cnobile2012/Li-IonBatteryProtection/LTSpice/Li-IonBatteryProtection.asc

C1: cap; 0.1µf
C2: cap; 0.22µf
C3: cap; 0.001µf
C4: cap; 47µf
D1: schottky; 1N5819
D2: schottky; 1N5819
D3: schottky; 1N5819
D4: schottky; 1N5819
Q1: npn2; 2N2222
Q2: npn2; 2N2222
Q3: npn2; 2N2222
Q4: npn2; 2N2222
Q5: npn2; 2N2222
Q6: IRF540; irf540n
R1: res; 10k
R2: res; 1k; tol=1 pwr=0.1
R3: res; 620k; tol=1 pwr=0.1
R4: res; 47k
R5: res; 100k; tol=1 pwr=0.1
R6: res; 100
R7: res; 120
R8: res; 10k
R9: res; 620k
R10: res; 1k
R11: res; 47k
R12: res; 100k
R13: res; 100
R14: res; 120
R15: res; 10k
R16: res; 1k
R17: res; 620k
R18: res; 47k
R19: res; 100k
R20: res; 100
R21: res; 120
R22: res; 10k
R23: res; 1k
R24: res; 620k
R25: res; 47k
R26: res; 100k
R27: res; 100
R28: res; 120
R29: res; 5.1k
R30: res; 3.3k
R31: res; 20k
RLoad: res; 2
U1: LM311
U2: PC817C
U3: LM311
U4: PC817C
U5: PC817C
U6: LM311
U7: PC817C
U8: LM311
V1: voltage; PULSE(3.6 0 0 1 0 0 1 1)
V2: voltage; PULSE(3.6 0 0 1 0 0 1 2)
V3: voltage; PULSE(3.6 0 0 1 0 0 1 3)
V4: voltage; PULSE(3.6 0 0 1 0 0 1 4)
Z1: zener; 1N4728
Z2: zener; 1N4728
Z3: zener; 1N4728
Z4: zener; 1N4728
Named nets: 0, Sawtooth-1, Output-V, Output+V, -Comp-1, +Comp-1, Bias-1, TP-Q1, Out-U1, Sawtooth-2, Out-U2, -Comp-2, +Comp-2, TP-Q2, Bias-2, Bias-3, Sawtooth-3, Out-U3, -Comp-3, +Comp-3, TP-Q3, Sawtooth-4, Out-U4, -Comp-4, +Comp-4, TP-Q4
.inc irf540n.sub
.tran 4010m
.inc PC817.sub
.inc LM311.sub
R31 -- 14.4V = 20k, 7.2V = 6.2k
R9 -- 14.4V = 3.3k, 7.2V = 1.8K
16.6 mA through all optos
Li-Ion Battery Protector
Carl J. Nobile
2017-08-21
